MOSH-Insa-Toulouse/ISS-2023-Gas-Sensor-AJB-RM/Image/Authentification_and_transmission.png

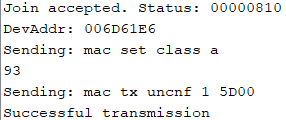
Image/Authentification_and_transmission.png
