MOSH-Insa-Toulouse/ISS-2023-Gas-Sensor-AJB-RM/ltspice-stuff/conditionneur_signal_gaz_sensor.PNG

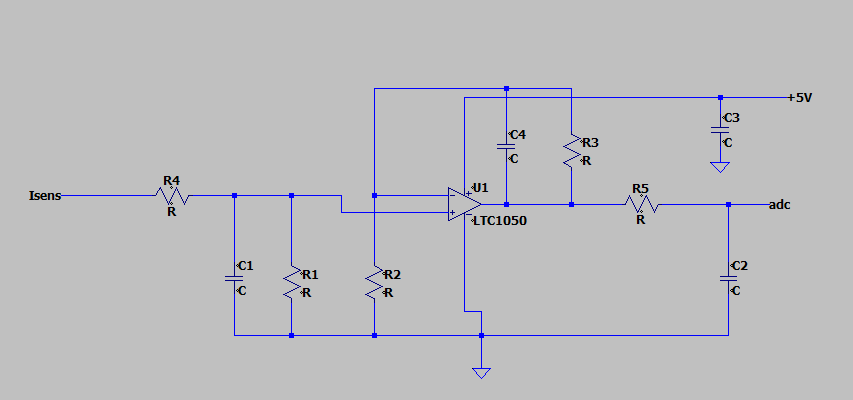
ltspice-stuff/conditionneur_signal_gaz_sensor.PNG
