MOSH-Insa-Toulouse/ISS-2023-Gas-Sensor-AJB-RM/ltspice-stuff/bruit_50hz.asc

C1: cap; 100n
C2: cap; 100n
C3: cap; 100n
C4: cap; 1µ
I1: current; PULSE(50n 100n 1 0.1 0.1 2); AC 1 0
R1: res; 100k
R2: res; 1k
R3: res; 100k
R4: res; 10k
R5: res; 1k
U1: LTC1050
V1: voltage; 5; AC 1 0
V2: voltage; PULSE(0 1 0.2 0.1 0.1 20)
X1: gas_sensor
Named nets: adc, 0, +5V, v-, v+
;tran 4
;tran 4
.ac dec 100 1 1G
