MOSH-Insa-Toulouse/ISS-2023-Gas-Sensor-AJB-RM/ltspice-stuff/calcul-r-sensor.asc

C1: cap; 100n
C2: cap; 100n
C3: cap; 1p
C4: cap; 1µ
R1: res; 100k
R2: res; 1k
R3: res; 100k
R4: res; 10k
R5: res; 1k
U1: LTC1050
V1: voltage; 5; AC 1 0
V2: voltage; PULSE(0 1 0.2 0.1 0.1 20); AC 1
V3: voltage; SINE(0 325 50); AC 1
X2: smiley
Named nets: adc, 0, +5V, v-, v+
;tran 2
;tran 4
.ac dec 100 1 10G
