MOSH-Insa-Toulouse/ISS-2023-Gas-Sensor-AJB-RM/ltspice-stuff/gas_sensor.asc

B1: bi; I=V(cp,cn)*(10n+(v(gc,gn)*10n))
C1: cap; 200µ
R1: res; 1k
Named nets: gp, gn, cp, cn, gc
